jaysonlarose/IR-Buddy/firmware/src/Arduino-IRremote2/IRremote.h

//******************************************************************************
// IRremote
// Version 2.0.1 June, 2015
// Copyright 2009 Ken Shirriff
// For details, see http://arcfn.com/2009/08/multi-protocol-infrared-remote-library.html
// Edited by Mitra to add new controller SANYO
//
// Interrupt code based on NECIRrcv by Joe Knapp
// http://www.arduino.cc/cgi-bin/yabb2/YaBB.pl?num=1210243556
// Also influenced by http://zovirl.com/2008/11/12/building-a-universal-remote-with-an-arduino/
//
// JVC and Panasonic protocol added by Kristian Lauszus (Thanks to zenwheel and other people at the original blog post)
// LG added by Darryl Smith (based on the JVC protocol)
// Whynter A/C ARC-110WD added by Francesco Meschia
//******************************************************************************

#ifndef IRremote_h
#define IRremote_h

//------------------------------------------------------------------------------
// The ISR header contains several useful macros the user may wish to use
//
#include "IRremoteInt.h"


//------------------------------------------------------------------------------
// Set DEBUG to 1 for lots of lovely debug output
//
#define DEBUG  0

//------------------------------------------------------------------------------
// Debug directives
//
#if DEBUG
#	define DBG_PRINT(...)    Serial.print(__VA_ARGS__)
#	define DBG_PRINTLN(...)  Serial.println(__VA_ARGS__)
#else
#	define DBG_PRINT(...)
#	define DBG_PRINTLN(...)
#endif

//------------------------------------------------------------------------------
// Mark & Space matching functions
//
int  MATCH       (int measured, int desired) ;
int  MATCH_MARK  (int measured_ticks, int desired_us) ;
int  MATCH_SPACE (int measured_ticks, int desired_us) ;

//------------------------------------------------------------------------------
// Results returned from the decoder
//
class decode_results
{
	public:
		volatile unsigned int  *rawbuf;      // Raw intervals in 50uS ticks
		uint16_t               rawlen;       // Number of records in rawbuf
		uint8_t                overflow;     // true iff IR raw code too long
};

//------------------------------------------------------------------------------
// Decoded value for NEC when a repeat code is received
//
#define REPEAT 0xFFFFFFFF

//------------------------------------------------------------------------------
// Main class for receiving IR
//
class IRrecv
{
	public:
		IRrecv (int recvpin) ;
		IRrecv (int recvpin, int blinkpin);

		void  blink13    (int blinkflag) ;
		int   decode     (decode_results *results) ;
		void  enableIRIn ( ) ;
		bool  isIdle     ( ) ;
		void  resume     ( ) ;
		void  pause      ( ) ;


} ;

//------------------------------------------------------------------------------
// Main class for sending IR
//
class IRsend
{
	public:
		IRsend () { }

		void  custom_delay_usec (unsigned long uSecs);
		void  enableIROut 		(uint8_t khz) ;

} ;

#endif
